a1k0n/autorustler/lcd/font.cc

#include "./lcd.h"

// font stolen from
// http://dlnmh9ip6v2uc.cloudfront.net/datasheets/LCD/Monochrome/Nokia_5110_Example.pde

const uint8_t LCD::font[][5] = {
  {0x00, 0x00, 0x00, 0x00, 0x00},  // 20 space
  {0x00, 0x00, 0x5f, 0x00, 0x00},  // 21 !
  {0x00, 0x07, 0x00, 0x07, 0x00},  // 22 "
  {0x14, 0x7f, 0x14, 0x7f, 0x14},  // 23 #
  {0x24, 0x2a, 0x7f, 0x2a, 0x12},  // 24 $
  {0x23, 0x13, 0x08, 0x64, 0x62},  // 25 %
  {0x36, 0x49, 0x55, 0x22, 0x50},  // 26 &
  {0x00, 0x05, 0x03, 0x00, 0x00},  // 27 '
  {0x00, 0x1c, 0x22, 0x41, 0x00},  // 28 (
  {0x00, 0x41, 0x22, 0x1c, 0x00},  // 29 )
  {0x14, 0x08, 0x3e, 0x08, 0x14},  // 2a *
  {0x08, 0x08, 0x3e, 0x08, 0x08},  // 2b +
  {0x00, 0x50, 0x30, 0x00, 0x00},  // 2c ,
  {0x08, 0x08, 0x08, 0x08, 0x08},  // 2d -
  {0x00, 0x60, 0x60, 0x00, 0x00},  // 2e .
  {0x20, 0x10, 0x08, 0x04, 0x02},  // 2f /
  {0x3e, 0x51, 0x49, 0x45, 0x3e},  // 30 0
  {0x00, 0x42, 0x7f, 0x40, 0x00},  // 31 1
  {0x42, 0x61, 0x51, 0x49, 0x46},  // 32 2
  {0x21, 0x41, 0x45, 0x4b, 0x31},  // 33 3
  {0x18, 0x14, 0x12, 0x7f, 0x10},  // 34 4
  {0x27, 0x45, 0x45, 0x45, 0x39},  // 35 5
  {0x3c, 0x4a, 0x49, 0x49, 0x30},  // 36 6
  {0x01, 0x71, 0x09, 0x05, 0x03},  // 37 7
  {0x36, 0x49, 0x49, 0x49, 0x36},  // 38 8
  {0x06, 0x49, 0x49, 0x29, 0x1e},  // 39 9
  {0x00, 0x36, 0x36, 0x00, 0x00},  // 3a :
  {0x00, 0x56, 0x36, 0x00, 0x00},  // 3b ;
  {0x08, 0x14, 0x22, 0x41, 0x00},  // 3c <
  {0x14, 0x14, 0x14, 0x14, 0x14},  // 3d =
  {0x00, 0x41, 0x22, 0x14, 0x08},  // 3e >
  {0x02, 0x01, 0x51, 0x09, 0x06},  // 3f ?
  {0x32, 0x49, 0x79, 0x41, 0x3e},  // 40 @
  {0x7e, 0x11, 0x11, 0x11, 0x7e},  // 41 A
  {0x7f, 0x49, 0x49, 0x49, 0x36},  // 42 B
  {0x3e, 0x41, 0x41, 0x41, 0x22},  // 43 C
  {0x7f, 0x41, 0x41, 0x22, 0x1c},  // 44 D
  {0x7f, 0x49, 0x49, 0x49, 0x41},  // 45 E
  {0x7f, 0x09, 0x09, 0x09, 0x01},  // 46 F
  {0x3e, 0x41, 0x49, 0x49, 0x7a},  // 47 G
  {0x7f, 0x08, 0x08, 0x08, 0x7f},  // 48 H
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
  {0x78, 0x46, 0x41, 0x46, 0x78}   // 7f DEL
};
