a1k0n/autorustler/lcd/lcdtest.cc

#include <math.h>
#include <stdint.h>
#include <stdio.h>
#include <unistd.h>
#include "./gpio.h"
#include "./lcd.h"
#include "./spi.h"

const float aspect = 1.175f;

int main() {
  if (!gpio_init())
    return 1;
  LCD lcd;
  if (!lcd.Init()) {
    fprintf(stderr, "lcd init fail!");
    return 1;
  }

  uint8_t screen[84*6];
  int t = 0;
  for (;; t++) {
    int idx = 0;
    float r = 10*sin(t*0.1) + 22;
    for (int y = 0; y < 48; y += 8) {
      for (int x = 0; x < 84; x++) {
        uint8_t b = 0;
        for (int yy = 0; yy < 8; yy++) {
          b >>= 1;
          if ((y+yy-24)*(y+yy-24)*aspect*aspect + (x-42)*(x-42) < r*r) {
            if ((x+yy+t)&1)
              b |= 0x80;
          }
          if ((y+yy-24)*(y+yy-24)*aspect*aspect + (x-42)*(x-42) < r*r/2) {
            b |= 0x80;
          }
        }
        screen[idx++] = b;
      }
    }
    LCD::WriteString(42 - r, 16, "Hello, world!", screen);
    lcd.GotoXY(0, 0);
    lcd.Draw(screen, 84*6);
    usleep(30000);
  }
}
